justinb4003/crpc/output/slim80_cr_nofanplate_cord_hole_53mm.step

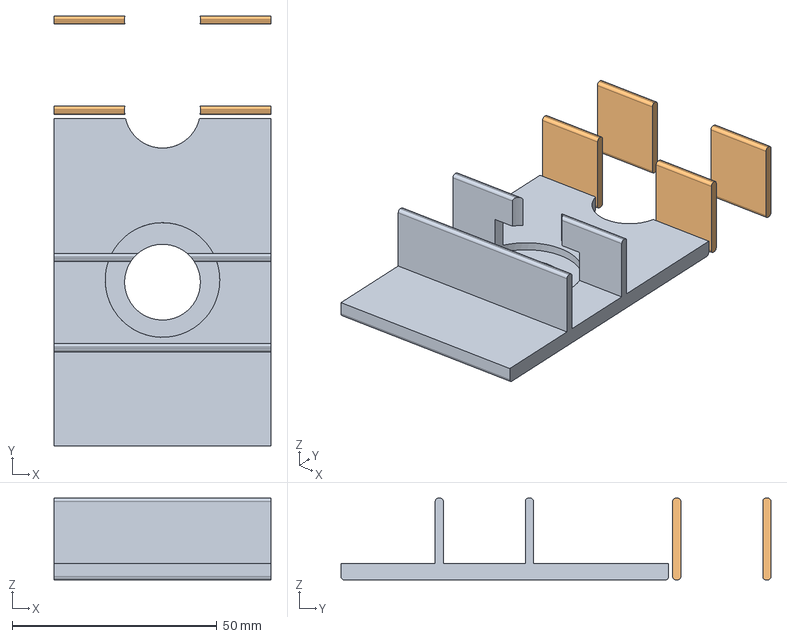
[picture p15: CAD file, 2023-04-13]
output/slim80_cr_nofanplate_cord_hole_53mm.step
53.0 x 105.0 x 20.0 mm
