justinb4003/crpc/output/slim80_cr_nofanplate_25mm.step

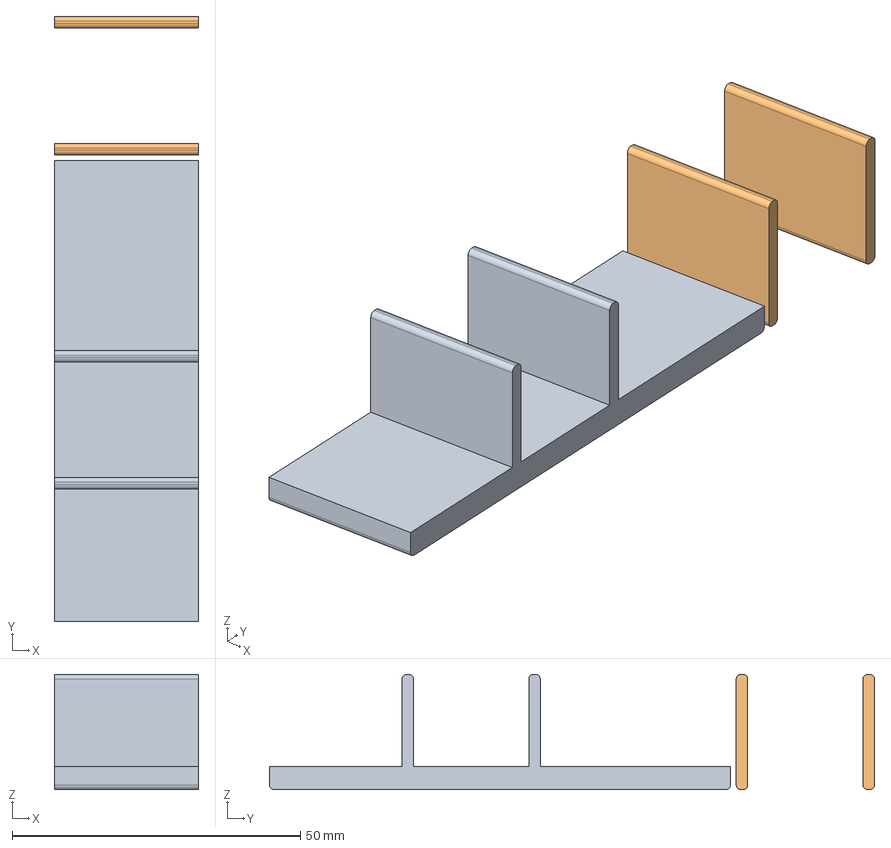
[picture p16: CAD file, 2023-04-13]
output/slim80_cr_nofanplate_25mm.step
25.0 x 105.0 x 20.0 mm
