justinb4003/crpc/output/slim80_cr_corner_65mm.step

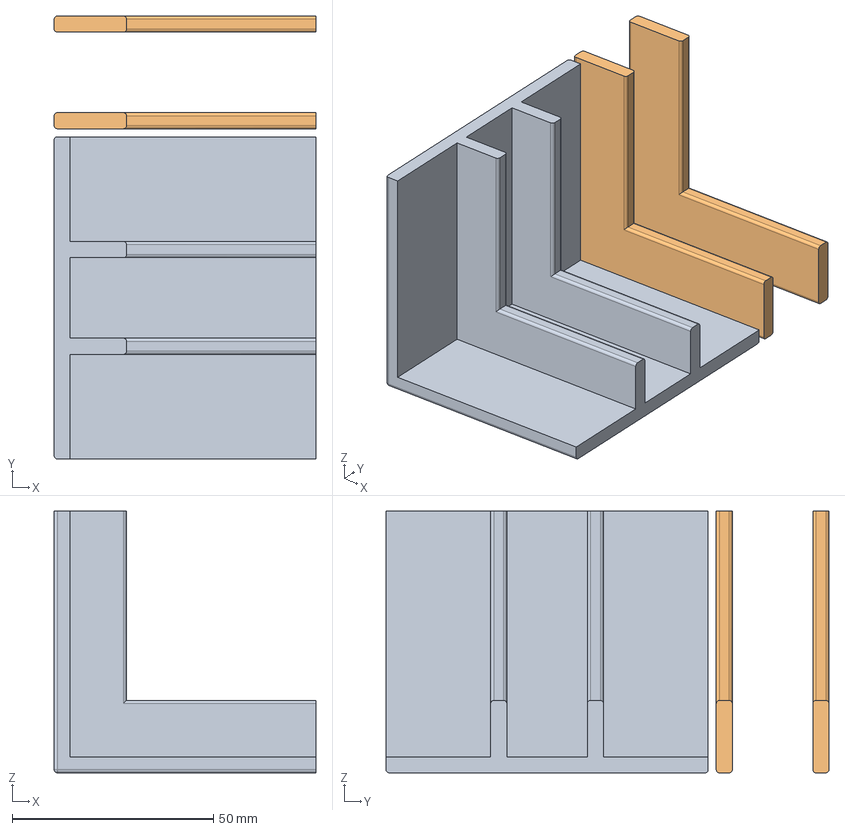
[picture p17: CAD file, 2023-04-13]
output/slim80_cr_corner_65mm.step
65.0 x 110.0 x 65.0 mm
