justinb4003/crpc/output/slim_cr_corner_50mm.step

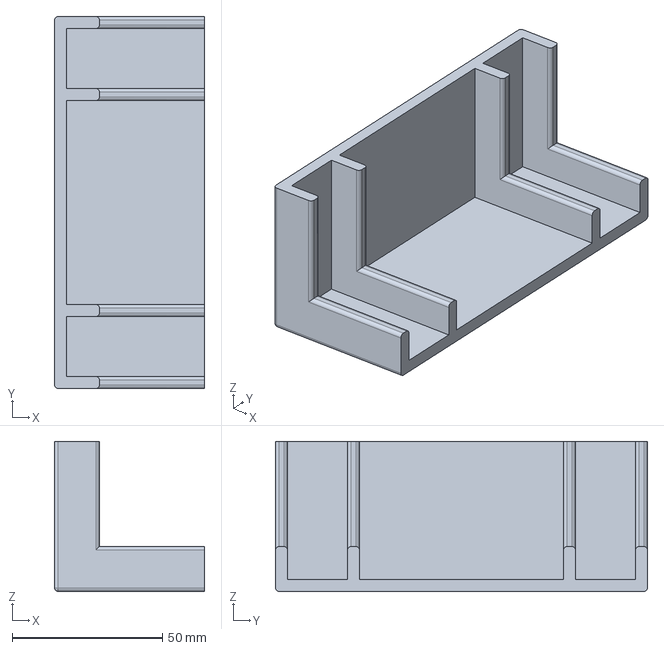
[picture p18: CAD file, 2023-04-13]
output/slim_cr_corner_50mm.step
50.0 x 124.0 x 50.0 mm
