justinb4003/crpc/output/slim_cr_nofanplate_cord_hole_51mm.step

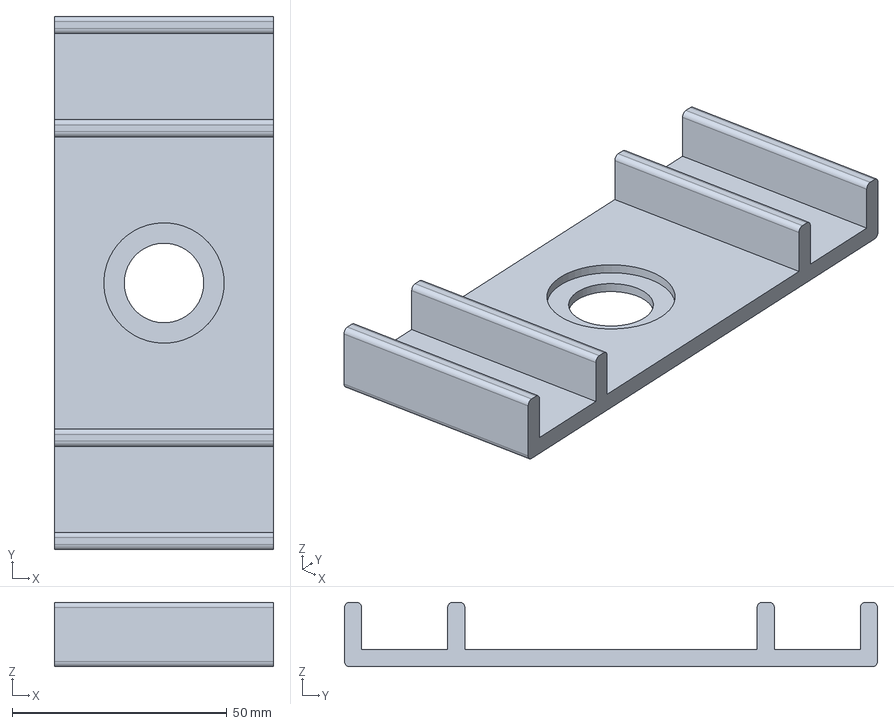
[picture p19: CAD file, 2023-04-13]
output/slim_cr_nofanplate_cord_hole_51mm.step
51.0 x 124.0 x 15.0 mm
