justinb4003/crpc/output/slim_cr_corner_30mm.step

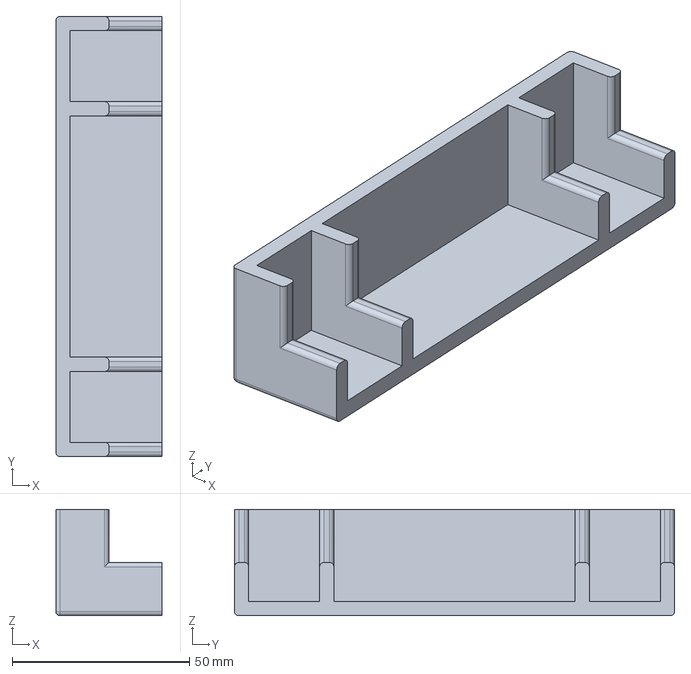
[picture p20: CAD file, 2023-04-13]
output/slim_cr_corner_30mm.step
30.0 x 124.0 x 30.0 mm
