justinb4003/crpc/output/slim80_cr_corner_100mm.step

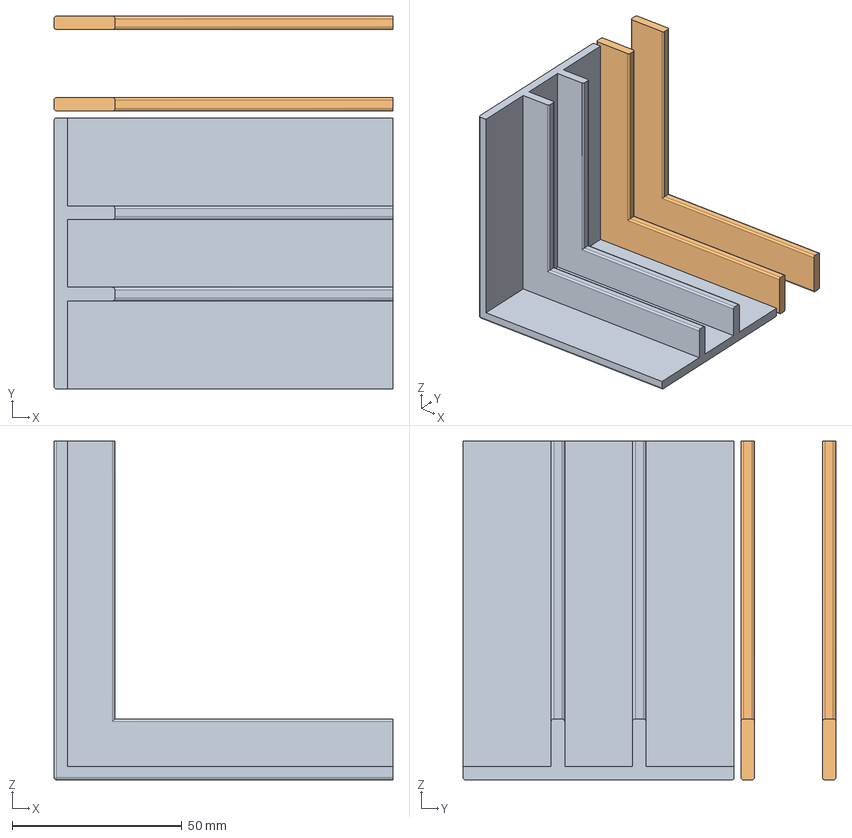
[picture p22: CAD file, 2023-04-13]
output/slim80_cr_corner_100mm.step
100.0 x 110.0 x 100.0 mm
