justinb4003/crpc/output/slim80_cr_corner_30mm.step

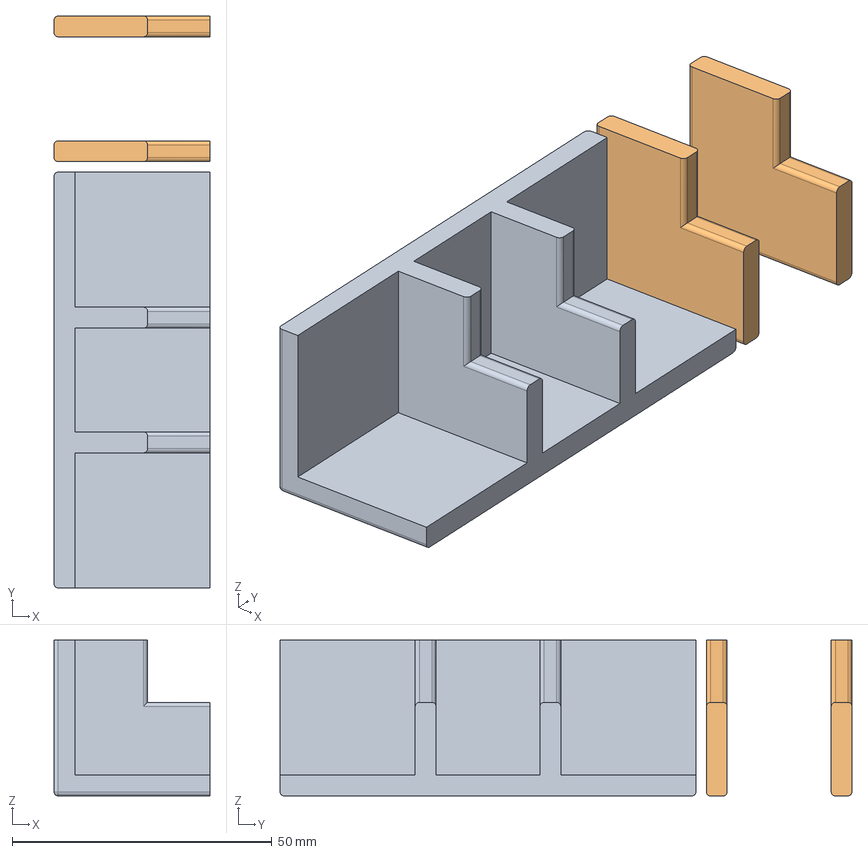
[picture p23: CAD file, 2023-04-13]
output/slim80_cr_corner_30mm.step
30.0 x 110.0 x 30.0 mm
