justinb4003/crpc/output/slim80_cr_nofanplate_51mm.step

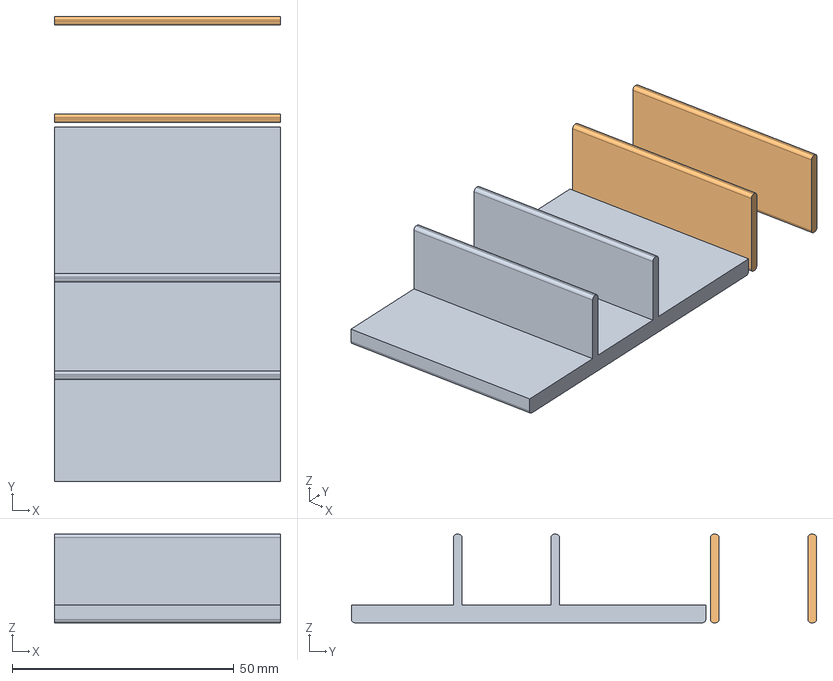
[picture p24: CAD file, 2023-04-13]
output/slim80_cr_nofanplate_51mm.step
51.0 x 105.0 x 20.0 mm
