justinb4003/crpc/output/slim_cr_corner_65mm.step

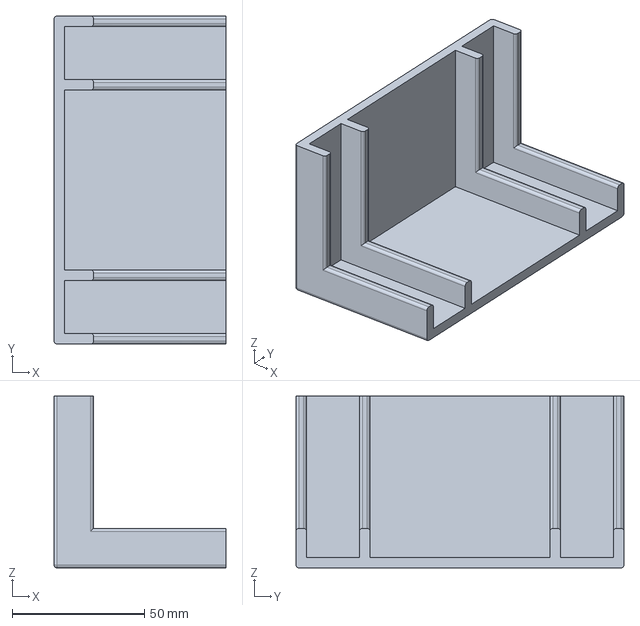
[picture p25: CAD file, 2023-04-13]
output/slim_cr_corner_65mm.step
65.0 x 124.0 x 65.0 mm
