justinb4003/crpc/output/slim_cr_nofanplate_20mm.step

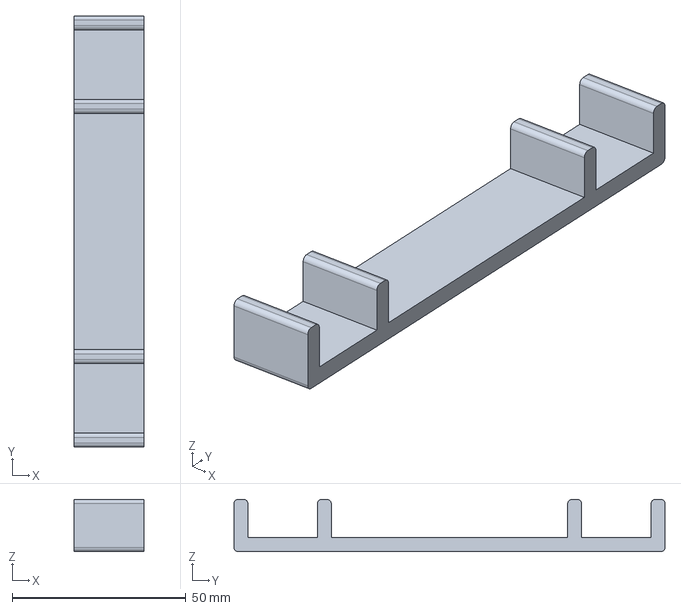
[picture p27: CAD file, 2023-04-09]
output/slim_cr_nofanplate_20mm.step
20.0 x 124.0 x 15.0 mm
