justinb4003/crpc/output/cr_fanplate_120mm.step

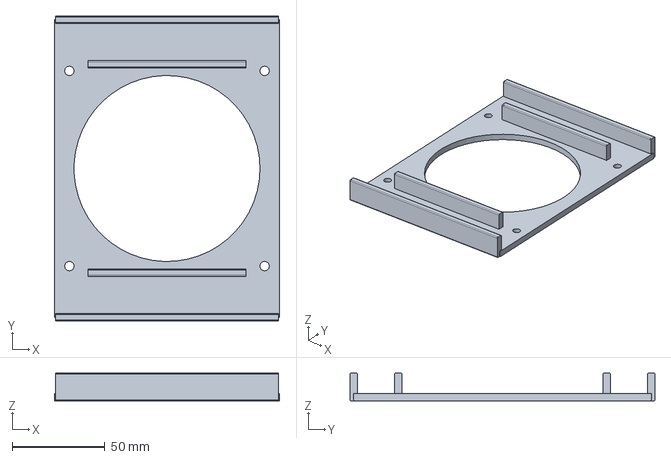
[picture p28: CAD file, 2023-02-26]
output/cr_fanplate_120mm.step
121.0 x 164.0 x 15.0 mm
