justinb4003/crpc/output/slim_cr_nofanplate_cord_hole_25mm.step

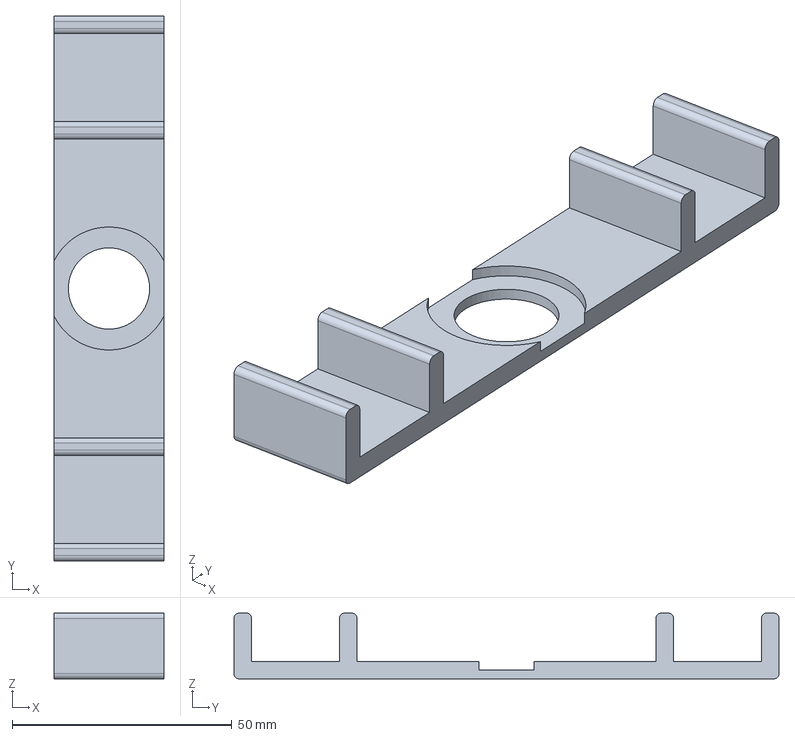
[picture p29: CAD file, 2023-02-26]
output/slim_cr_nofanplate_cord_hole_25mm.step
25.0 x 124.0 x 15.0 mm
