justinb4003/crpc/output/slim_cr_corner_37mm.step

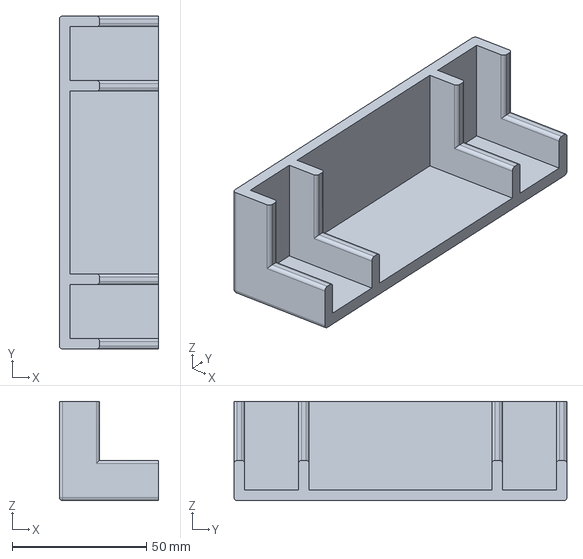
[picture p30: CAD file, 2023-02-26]
output/slim_cr_corner_37mm.step
37.0 x 124.0 x 37.0 mm
