justinb4003/crpc/output/cr_fanplate_121mm.step

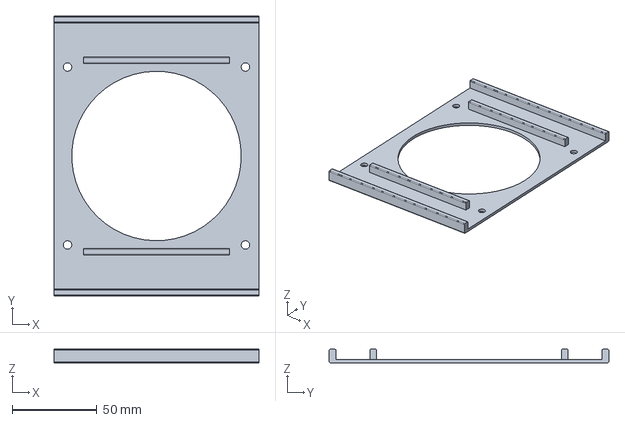
[picture p31: CAD file, 2023-02-26]
output/cr_fanplate_121mm.step
121.0 x 165.0 x 8.00 mm
