justinb4003/crpc/output/slim_cr_nofanplate_100mm.step

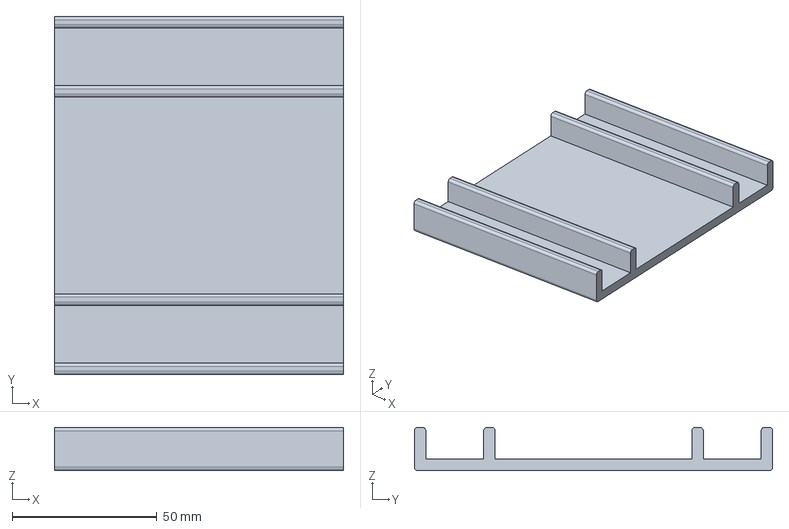
[picture p32: CAD file, 2023-02-26]
output/slim_cr_nofanplate_100mm.step
100.0 x 124.0 x 15.0 mm
