justinb4003/crpc/output/cr_corner_25mm.step

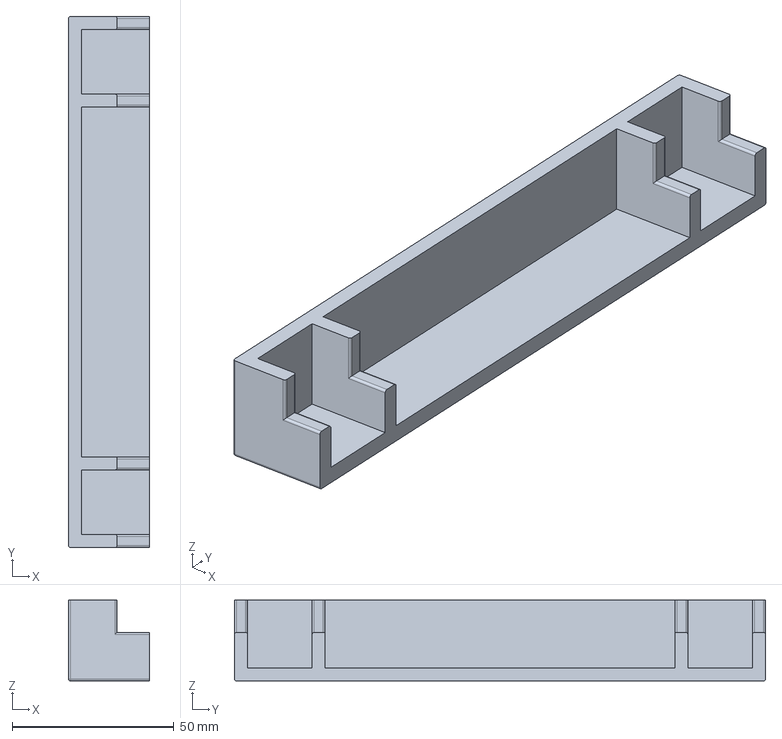
[picture p33: CAD file, 2023-02-26]
output/cr_corner_25mm.step
25.0 x 164.0 x 25.0 mm
