justinb4003/crpc/output/slim_cr_nofanplate_40mm.step

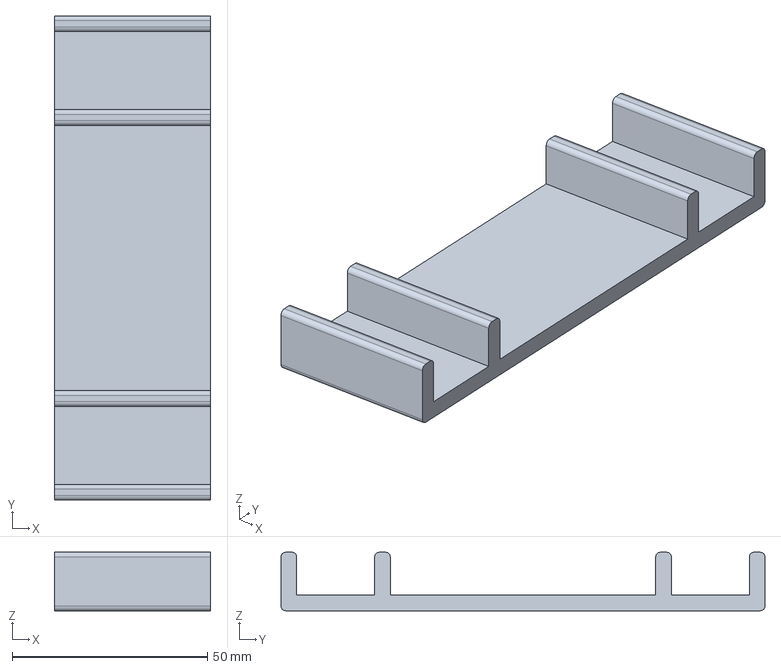
[picture p34: CAD file, 2023-02-26]
output/slim_cr_nofanplate_40mm.step
40.0 x 124.0 x 15.0 mm
