justinb4003/crpc/output/cr_corner_65mm.step

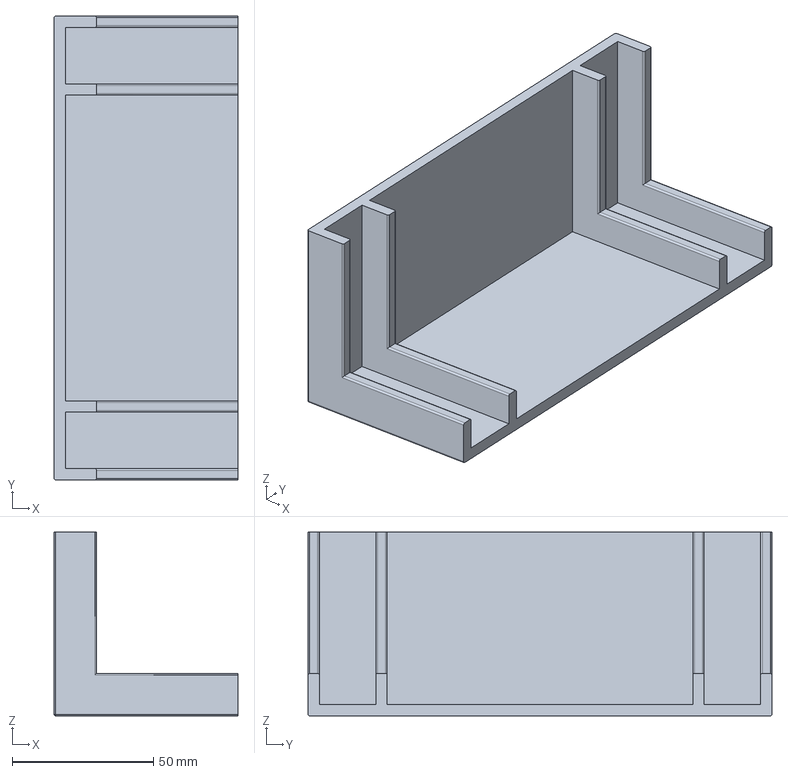
[picture p35: CAD file, 2023-02-26]
output/cr_corner_65mm.step
65.0 x 164.0 x 65.0 mm
