justinb4003/crpc/output/cr_nofanplate_25mm.step

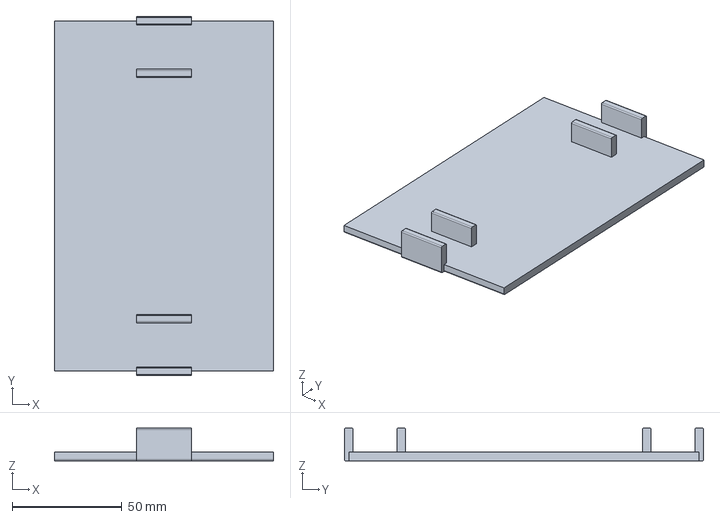
[picture p36: CAD file, 2023-02-26]
output/cr_nofanplate_25mm.step
100.0 x 164.0 x 15.0 mm
