justinb4003/crpc/output/cr_corner_50mm.step

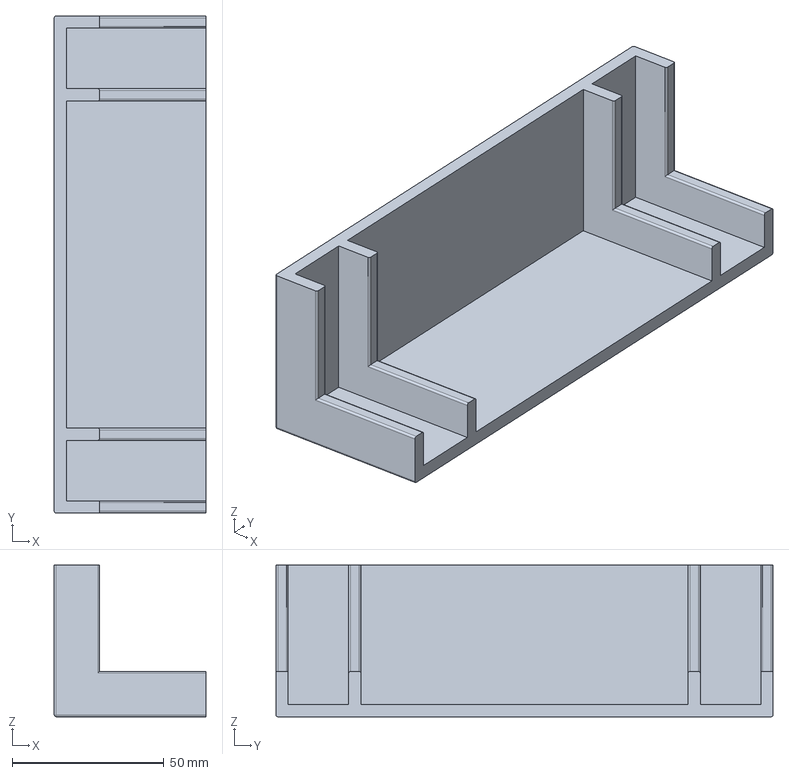
[picture p37: CAD file, 2023-02-26]
output/cr_corner_50mm.step
50.0 x 164.0 x 50.0 mm
