justinb4003/crpc/output/cr_nofanplate_100mm.step

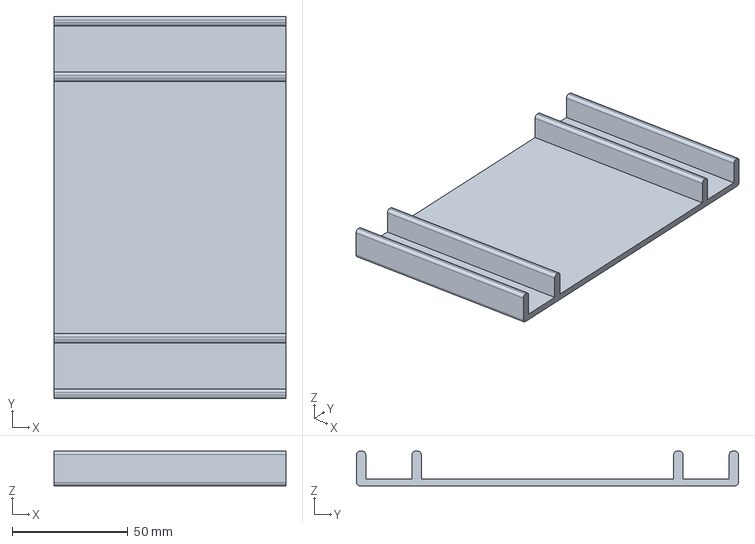
[picture p38: CAD file, 2023-01-20]
output/cr_nofanplate_100mm.step
100.0 x 165.0 x 15.0 mm
