justinb4003/crpc/output/cr_corner_100mm.step

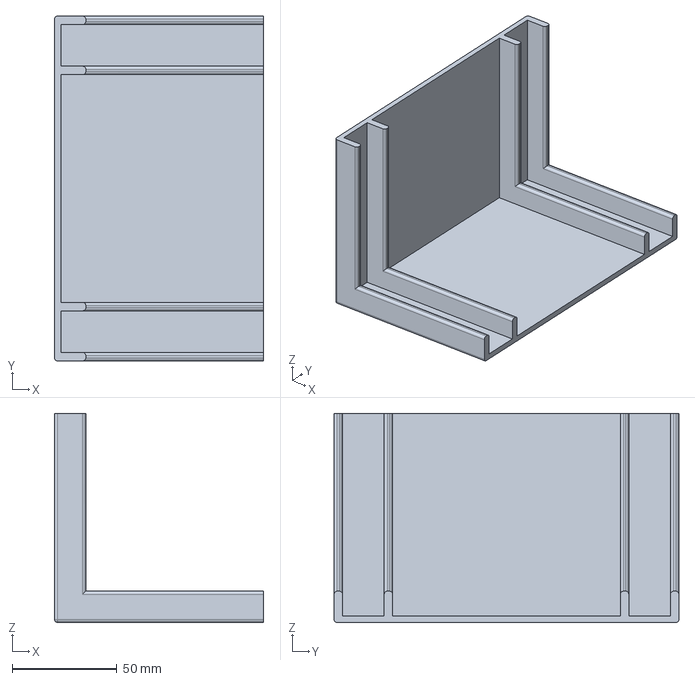
[picture p39: CAD file, 2023-01-20]
output/cr_corner_100mm.step
100.0 x 165.0 x 100.0 mm
